mickdassive/usbc_car_module/src/hub.cpp

//{usbc car module}
//{hub.cpp}
//Copyright (C) {2023}  {mickmake}
//
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
#ifndef hub_cpp
#define hub_cpp

#include <Arduino.h>
#include <Wire.h>
#include "hub.h"
#include "debug.h"


/**
 * Writes a 16-bit value to the hub register.
 * 
 * @param input The value to be written to the hub register.
 */
void hub_reg_write (uint16_t input) {

    debug_msg(partal_hub, "hub_reg_write called", true, input);

    //init local vars
    uint8_t hub_reg_msb = 0;
    uint8_t hub_reg_lsb = 0;

    hub_reg_lsb = input & 0x00FF;
    hub_reg_msb = (input >> 8) & 0x00FF;

    Wire.write(hub_reg_msb);
    Wire.write(hub_reg_lsb);
    return;
}

/**
 * Sends a reboot command to the hub.
 */
void hub_send_reset() {

    debug_msg(partal_hub, "hub_send_reset called restetting hub", false, 0);

    Wire.beginTransmission(hub_addr);
    hub_reg_write(0x9936);
    Wire.write(0x00);
    Wire.endTransmission();
    return;
}

/**
 * Sends a USB attach signal to the hub.
 */
void hub_send_usb_attach_with_smbus_active() {

    debug_msg(partal_hub, "hub_sen_usb_attach_with_smbus_active called moving hub into active mode wilth i2c interface active", false, 0);

    Wire.beginTransmission(hub_addr);
    hub_reg_write(0xAA56);
    Wire.write(0x00);
    Wire.endTransmission();
    return;
}

/**
 * Sends a command to register access command to the hub.
 */
void hub_send_command_register_access_command() {

    debug_msg(partal_hub, "hub_send_command_register_access_command called", false, 0);

    Wire.beginTransmission(hub_addr);
    hub_reg_write(0x9937);
    Wire.write(0x00);
    Wire.endTransmission();
    return;
}

/**
 * Sends a write command to the hub to perform OTP (One-Time Programmable) write operation.
 */
void hub_send_otp_write() {

    debug_msg(partal_hub, "hub_send_otp_write called", false, 0);

    Wire.beginTransmission(hub_addr);
    hub_reg_write(0x9933);
    Wire.write(0x00);
    Wire.endTransmission();
    return;
}

/**
 * Sends a command to the hub to read the OTP (One-Time Programmable) memory.
 */
void hub_send_otp_read() {

    debug_msg(partal_hub, "hub_send_otp_read called", false, 0);

    Wire.beginTransmission(hub_addr);
    hub_reg_write(0x9934);
    Wire.write(0x00);
    Wire.endTransmission();
    return;
}

/**
 * Initializes the hub by sending commands to configure various registers.
 * This function sets the default values for different hub registers.
 * 
 */
void hub_init() {

    debug_msg(partal_hub, "hub_init called, setting up defult values for hub", false, 0);

    hub_send_command_register_access_command();

    //begin writeing defult vlaues to hub 
    //clock_ctl register
    Wire.beginTransmission(hub_addr);
    hub_reg_write(hub_reg_clock_ctl);
    Wire.write(1);
    //prog guide page 15
    //(xtal_susp_dis, resv, resv, pll125_en, pll125_stable, rosc_en, pll60_en, resv)
    Wire.write(0b1000000);
    Wire.write(0x00);
    Wire.endTransmission();

    //util_config1 register
    Wire.beginTransmission(hub_addr);
    hub_reg_write(hub_reg_util_config1);
    Wire.write(1);
    //prog guide page 16
    //(resv, dev_reset, resv, resv, resv, spi_master_dis, resv, hub_resume_inhibit)
    Wire.write(0b0);
    Wire.write(0x00);
    Wire.endTransmission();

    //pf6_ctl register
    Wire.beginTransmission(hub_addr);
    hub_reg_write(hub_reg_pf6_ctl);
    Wire.write(1);
    //prog guide page 26
    //(resv, resv, resv, resv, resv, b2, b1, b0)
    Wire.write(0b00000011);
    Wire.write(0x00);
    Wire.endTransmission();

    //pf8_ctl register
    Wire.beginTransmission(hub_addr);
    hub_reg_write(hub_reg_pf8_ctl);
    Wire.write(1);
    //prog guide page 27
    //(resv, resv, resv, resv, resv, b2, b1, b0)
    Wire.write(0b00000010);
    Wire.write(0x00);
    Wire.endTransmission();

    //hub_cfg_1 register
    Wire.beginTransmission(hub_addr);
    hub_reg_write(hub_reg_hub_cfg_1);
    Wire.write(1);
    //prog guide page 30
    //(self_bus_power, vsm_disable, hs_disable, mtt_enable, eop_disable, current_sns_b1, current_sns_b0, port_pwr)
    Wire.write(0b11110011);
    Wire.write(0x00);
    Wire.endTransmission();
    
    //hub_cfg_2 register 
    Wire.beginTransmission(hub_addr);
    hub_reg_write(hub_reg_hub_cfg_2);
    Wire.write(1);
    //prog guide page 31
    //(resv, resv, oc_timer_b1, oc_timer_b0, compound, resv, resv, resv)
    Wire.write(0b00111000);
    Wire.write(0x00);
    Wire.endTransmission();

    //hub_cfg_3 register
    Wire.beginTransmission(hub_addr);
    hub_reg_write(hub_reg_hub_cfg_3);
    Wire.write(1);
    //prog guide page 32
    //(resv, resv, resv, resv, prtmap_en, bos_disable, resv, string_en)
    Wire.write(0b00000001);
    Wire.write(0x00);
    Wire.endTransmission();

    //usb2_nrd register
    Wire.beginTransmission(hub_addr);
    hub_reg_write(hub_reg_usb2_nrd);
    Wire.write(1);
    //prog guide page 33
    //(prt7, prt6, prt5, prt4, prt3, prt2, prt1, resv)
    Wire.write(0b01000000);
    Wire.write(0x00);
    Wire.endTransmission();

    //bc_en register 
    Wire.beginTransmission(hub_addr);
    hub_reg_write(hub_reg_bc_en);
    Wire.write(1);
    //prog guide page 35
    //(prt7, prt6, prt5, prt4, prt3, prt2, prt1, resv)
    Wire.write(0b11111110);
    Wire.write(0x00);
    Wire.endTransmission();

    //start_lockout_timer_reg register
    Wire.beginTransmission(hub_addr);
    hub_reg_write(hub_reg_start_lockout_timer_reg);
    Wire.write(1);
    //prog guide page 35
    //time in ms to allow overcurrent events when a device is connected 
    Wire.write(hub_over_current_lockout_bypas_time);
    Wire.write(0x00);
    Wire.endTransmission();

    //prt_swap register
    Wire.beginTransmission(hub_addr);
    hub_reg_write(hub_reg_prt_swap);
    Wire.write(1);
    //prog guide page 36
    //ports with swaped usb2.0 pairs
    //(prt7, prt6, prt5, prt4, prt3, prt2, prt1, prt0)
    Wire.write(0b01011100);
    Wire.write(0x00);
    Wire.endTransmission();

    //usb2_prt_remap_12 register
    Wire.beginTransmission(hub_addr);
    hub_reg_write(hub_reg_usb2_prt_remap_12);
    Wire.write(1);
    //prog guide page 36
    Wire.write(0x21);
    Wire.write(0x00);
    Wire.endTransmission();

    //usb2_prt_remap_34 register
    Wire.beginTransmission(hub_addr);
    hub_reg_write(hub_reg_usb2_prt_remap_34);
    Wire.write(1);
    //prog guide page 37
    Wire.write(0x43);
    Wire.write(0x00);
    Wire.endTransmission();

    //usb2_prt_remap_56 register
    Wire.beginTransmission(hub_addr);
    hub_reg_write(hub_reg_usb2_prt_remap_56);
    Wire.write(1);
    //prog guide page 38
    Wire.write(0x65);
    Wire.write(0x00);
    Wire.endTransmission();

    //usb2_prt_remap_7 register
    Wire.beginTransmission(hub_addr);
    hub_reg_write(hub_reg_usb2_prt_remap_7);
    Wire.write(1);
    //prog guide page 38
    Wire.write(0x07);
    Wire.write(0x00);
    Wire.endTransmission();

    //usb3_hub_ctl register
    Wire.beginTransmission(hub_addr);
    hub_reg_write(hub_reg_usb3_hub_ctl);
    Wire.write(1);
    //prog guide page 46
    //(resv, resv, scramble_en, gang_ovr_current, bus_powerd, resv, resv, resv)
    Wire.write(0b00100000);
    Wire.write(0x00);
    Wire.endTransmission();

    //usb3_hub_ctl2 register
    Wire.beginTransmission(hub_addr);
    hub_reg_write(hub_reg_usb3_hub_ctl2);
    Wire.write(1);
    //prog guide page 46
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

    //hub_cmd_stat register
    //this write moves the hub from config mode to run mode
    Wire.beginTransmission(hub_addr);
    hub_reg_write(hub_reg_hub_cmd_stat);
    Wire.write(1);
    //prog guide page 39
    Wire.write(0x01);
    Wire.write(0x00);
    Wire.endTransmission();

    //usb3_hub_ctl2 register
    //starts usb3 hub fugtionality
    Wire.beginTransmission(hub_addr);
    hub_reg_write(hub_reg_usb3_hub_ctl2);
    Wire.write(1);
    //prog guide page 46
    //(hub_ds_prop_rst_ctl, hub_u3_rmt_wkup_en, hub_u1_u2_exit_failed, hub_ping_to_500ms, hub_stall_ep0_halt, hub_ux_exit_ctrl, resv, usb3_hub_enable)
    Wire.write(0b11111101);
    Wire.write(0x00);
    Wire.endTransmission();

    //send config register access command
    hub_send_command_register_access_command();

    //allow i2c to stay active in runtime
    hub_send_usb_attach_with_smbus_active();

    debug_msg(partal_hub, "hub init complete", false, 0);



    return;
}


#endif // hub_cpp
